SteveMayze/atmega1608_dev/kicad/ATMega1608_Dev/fritzing-part/kicad_svg_plots/board_render.png

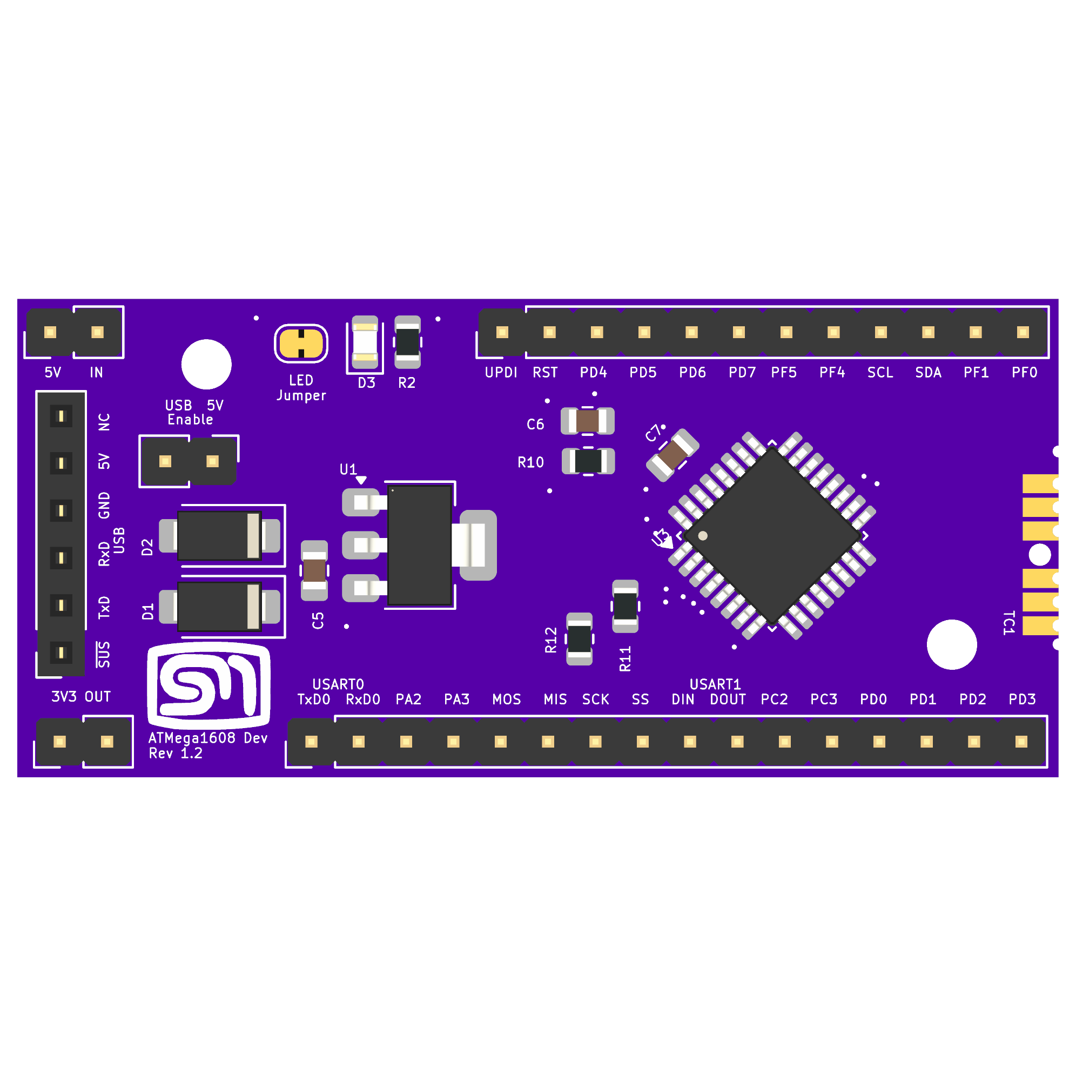
kicad/ATMega1608_Dev/fritzing-part/kicad_svg_plots/board_render.png
