SteveMayze/atmega1608_dev/kicad/doc/PinAllocation.png

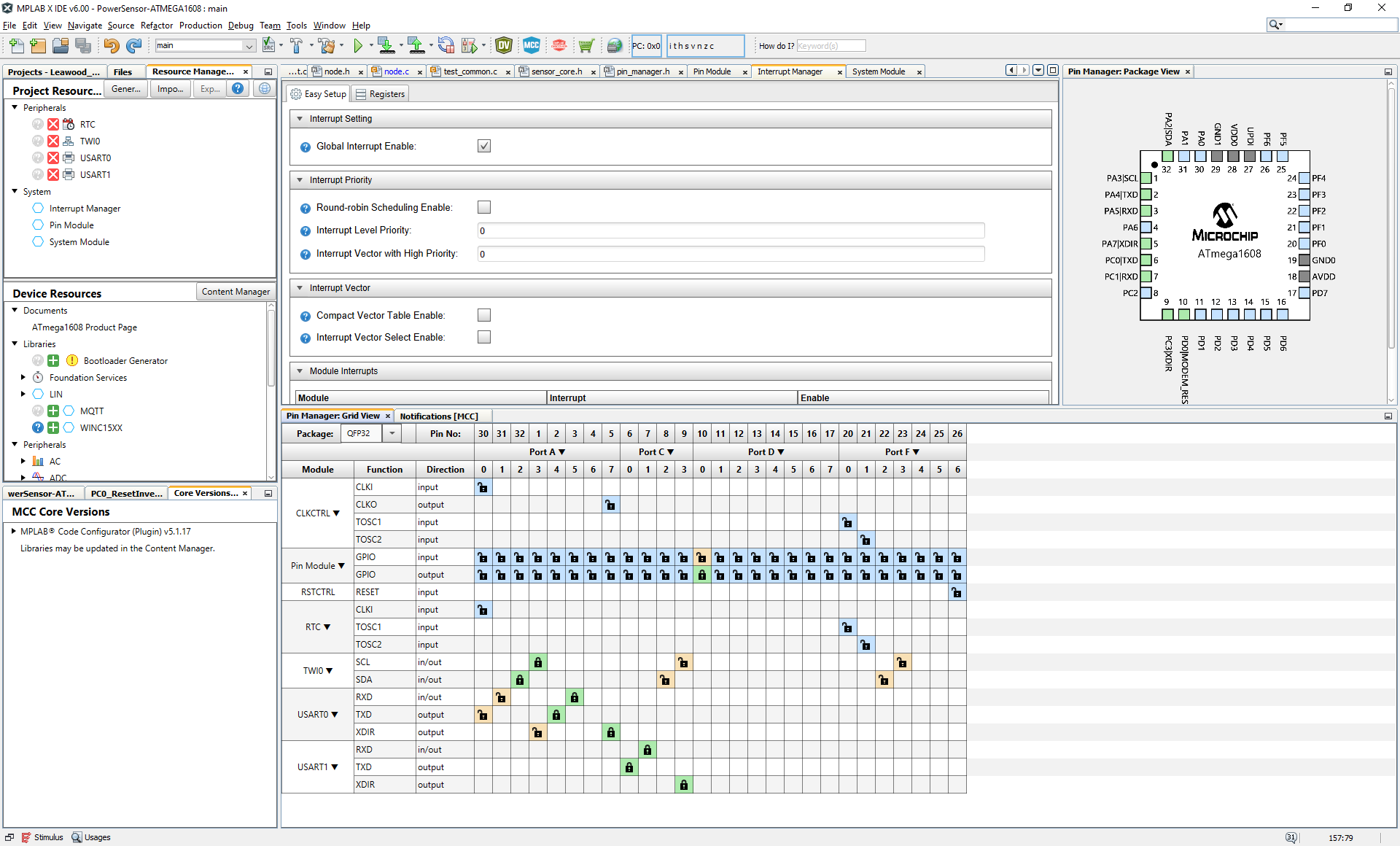
kicad/doc/PinAllocation.png
