SteveMayze/atmega1608_dev/kicad/doc/PinManagerTable.png

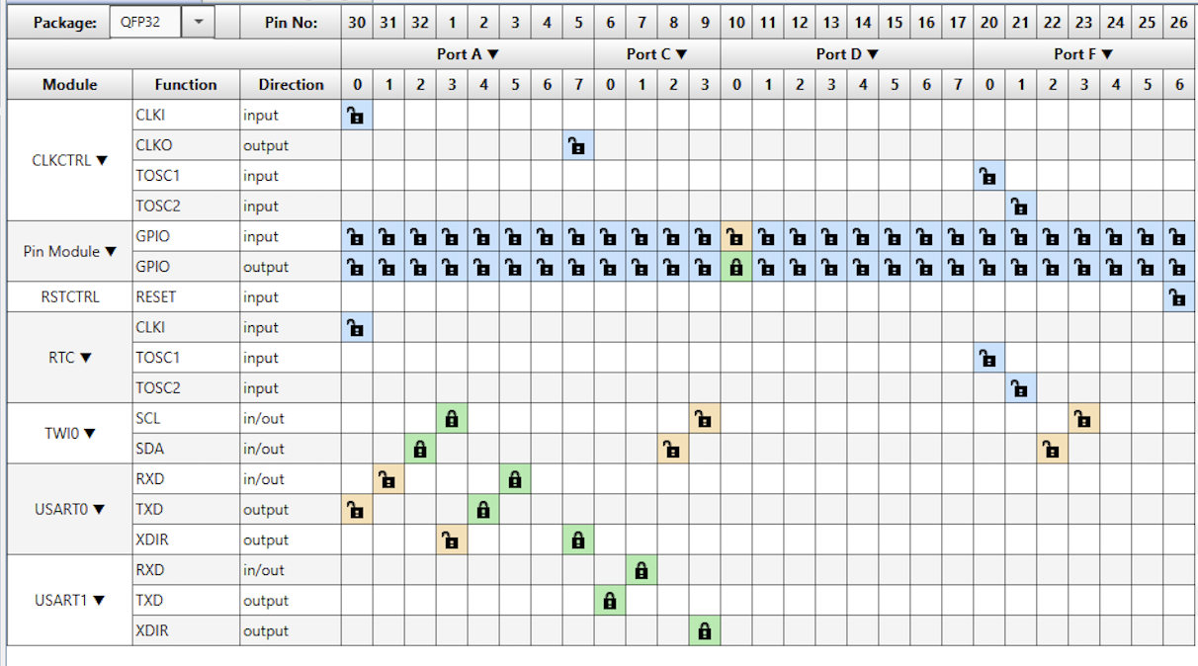
kicad/doc/PinManagerTable.png
