SteveMayze/atmega1608_dev/kicad/doc/USART-Troubleshooting/DeviceManager.png

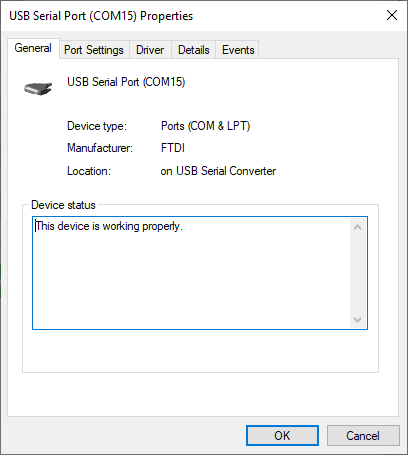
kicad/doc/USART-Troubleshooting/DeviceManager.png
