SteveMayze/atmega1608_dev/kicad/doc/USART-Troubleshooting/DeviceManager_02.png

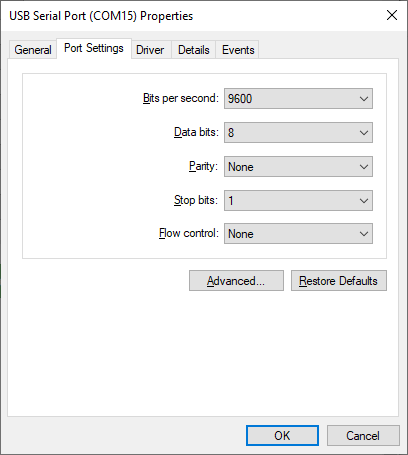
kicad/doc/USART-Troubleshooting/DeviceManager_02.png
