SteveMayze/atmega1608_dev/kicad/doc/USART-Troubleshooting/DeviceManager_03.png

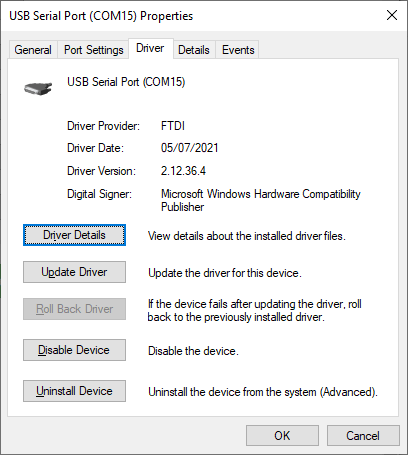
kicad/doc/USART-Troubleshooting/DeviceManager_03.png
