SteveMayze/atmega1608_dev/kicad/doc/CentralCommand-Layout.pdf

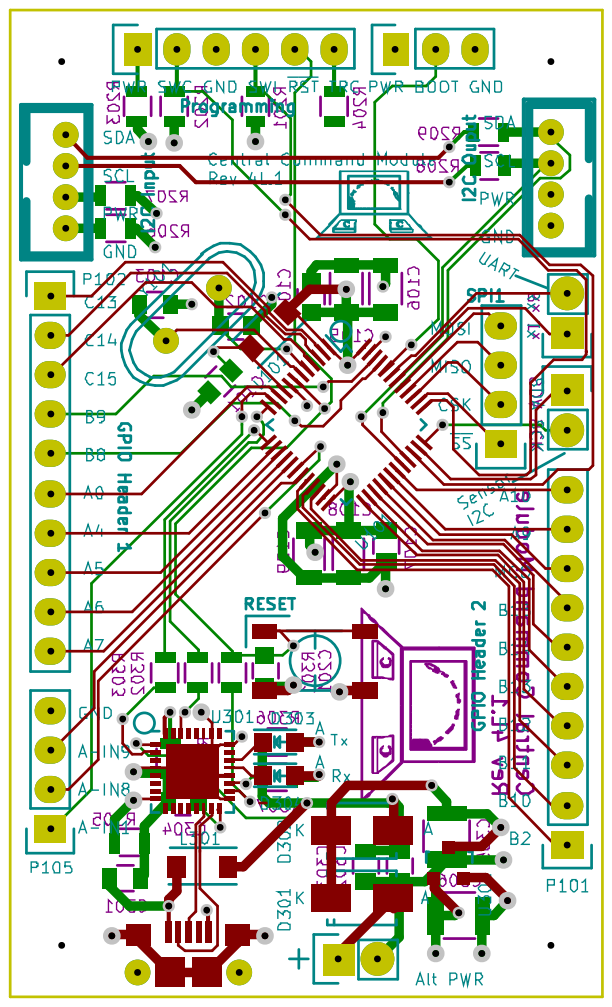
[picture p16: page 1]
