SteveMayze/atmega1608_dev/kicad/doc/SML-LX15IGC-RP-TR.pdf

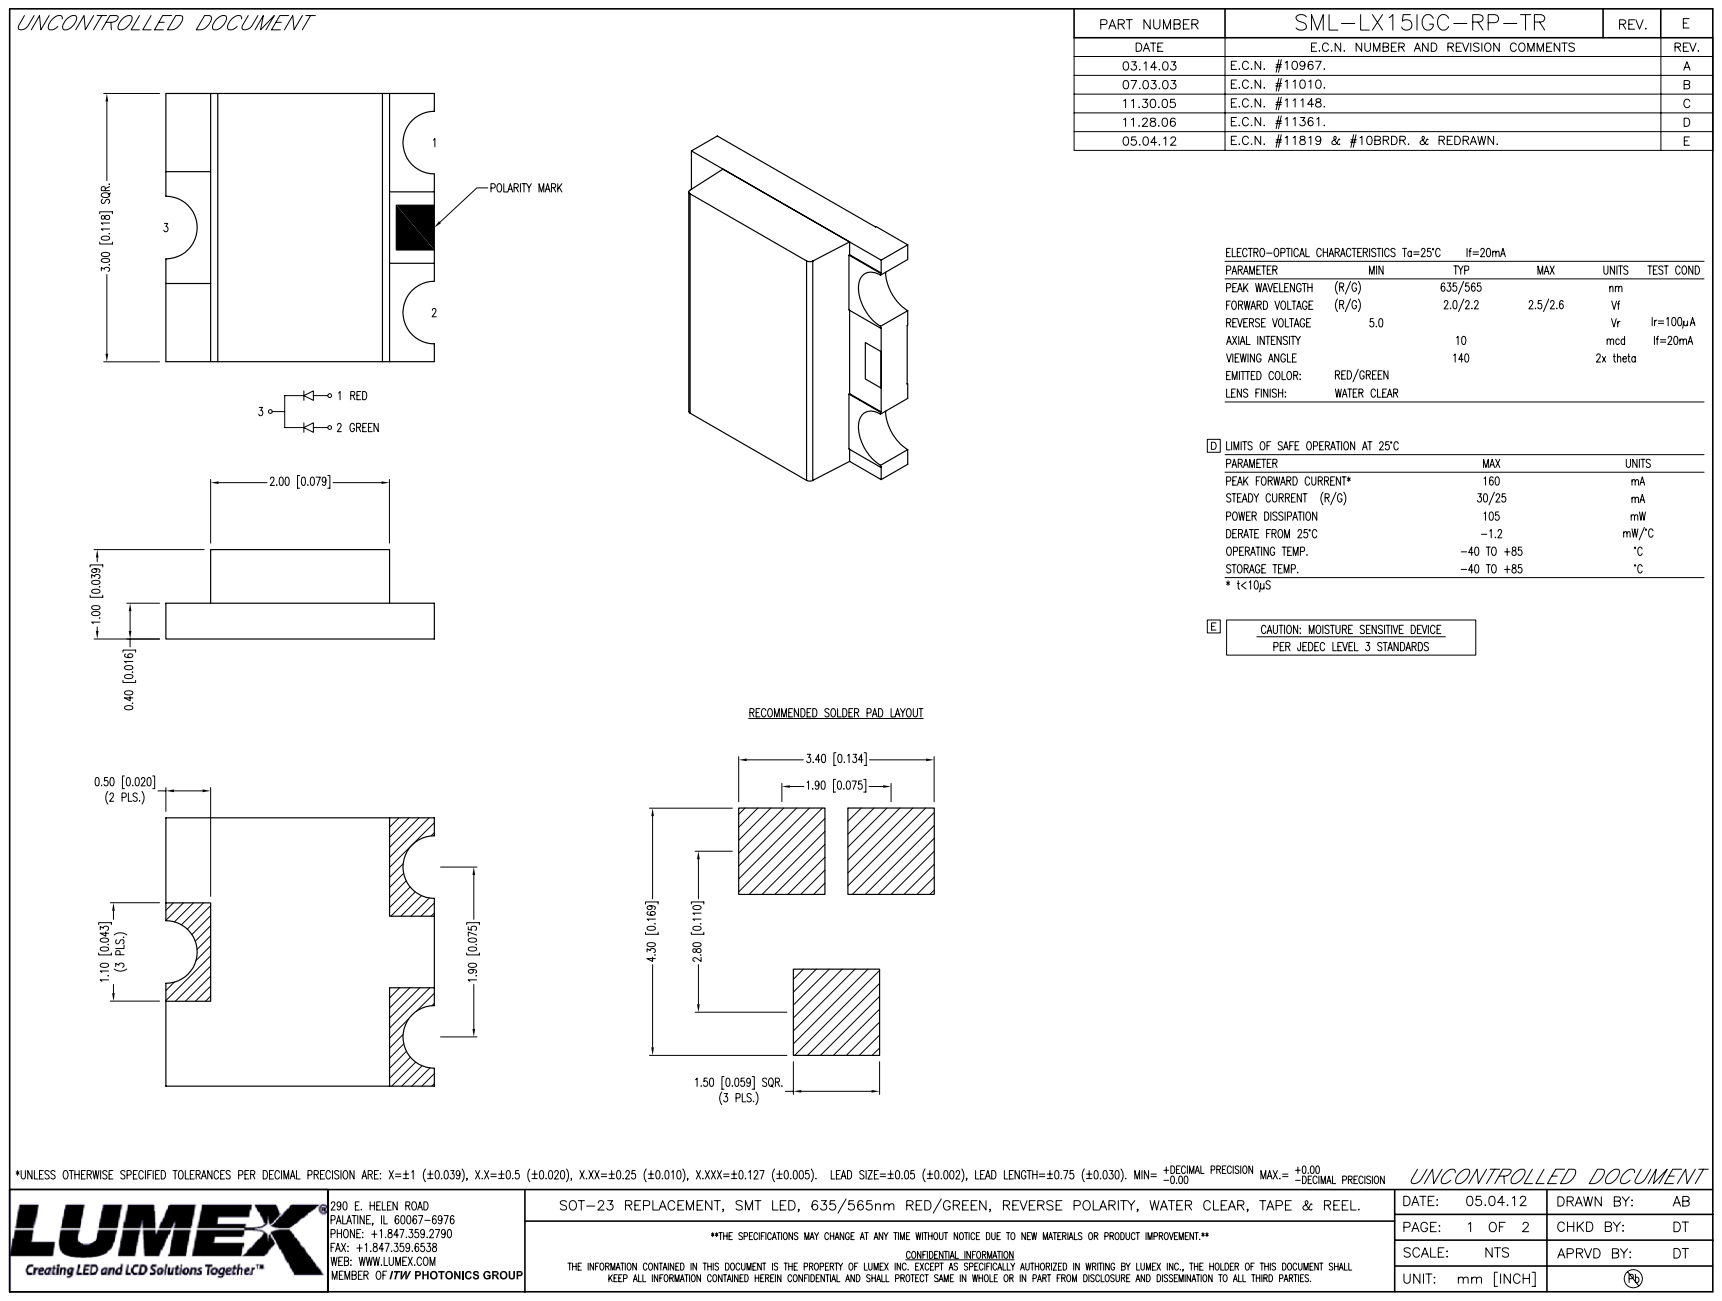
[picture p17: page 1]

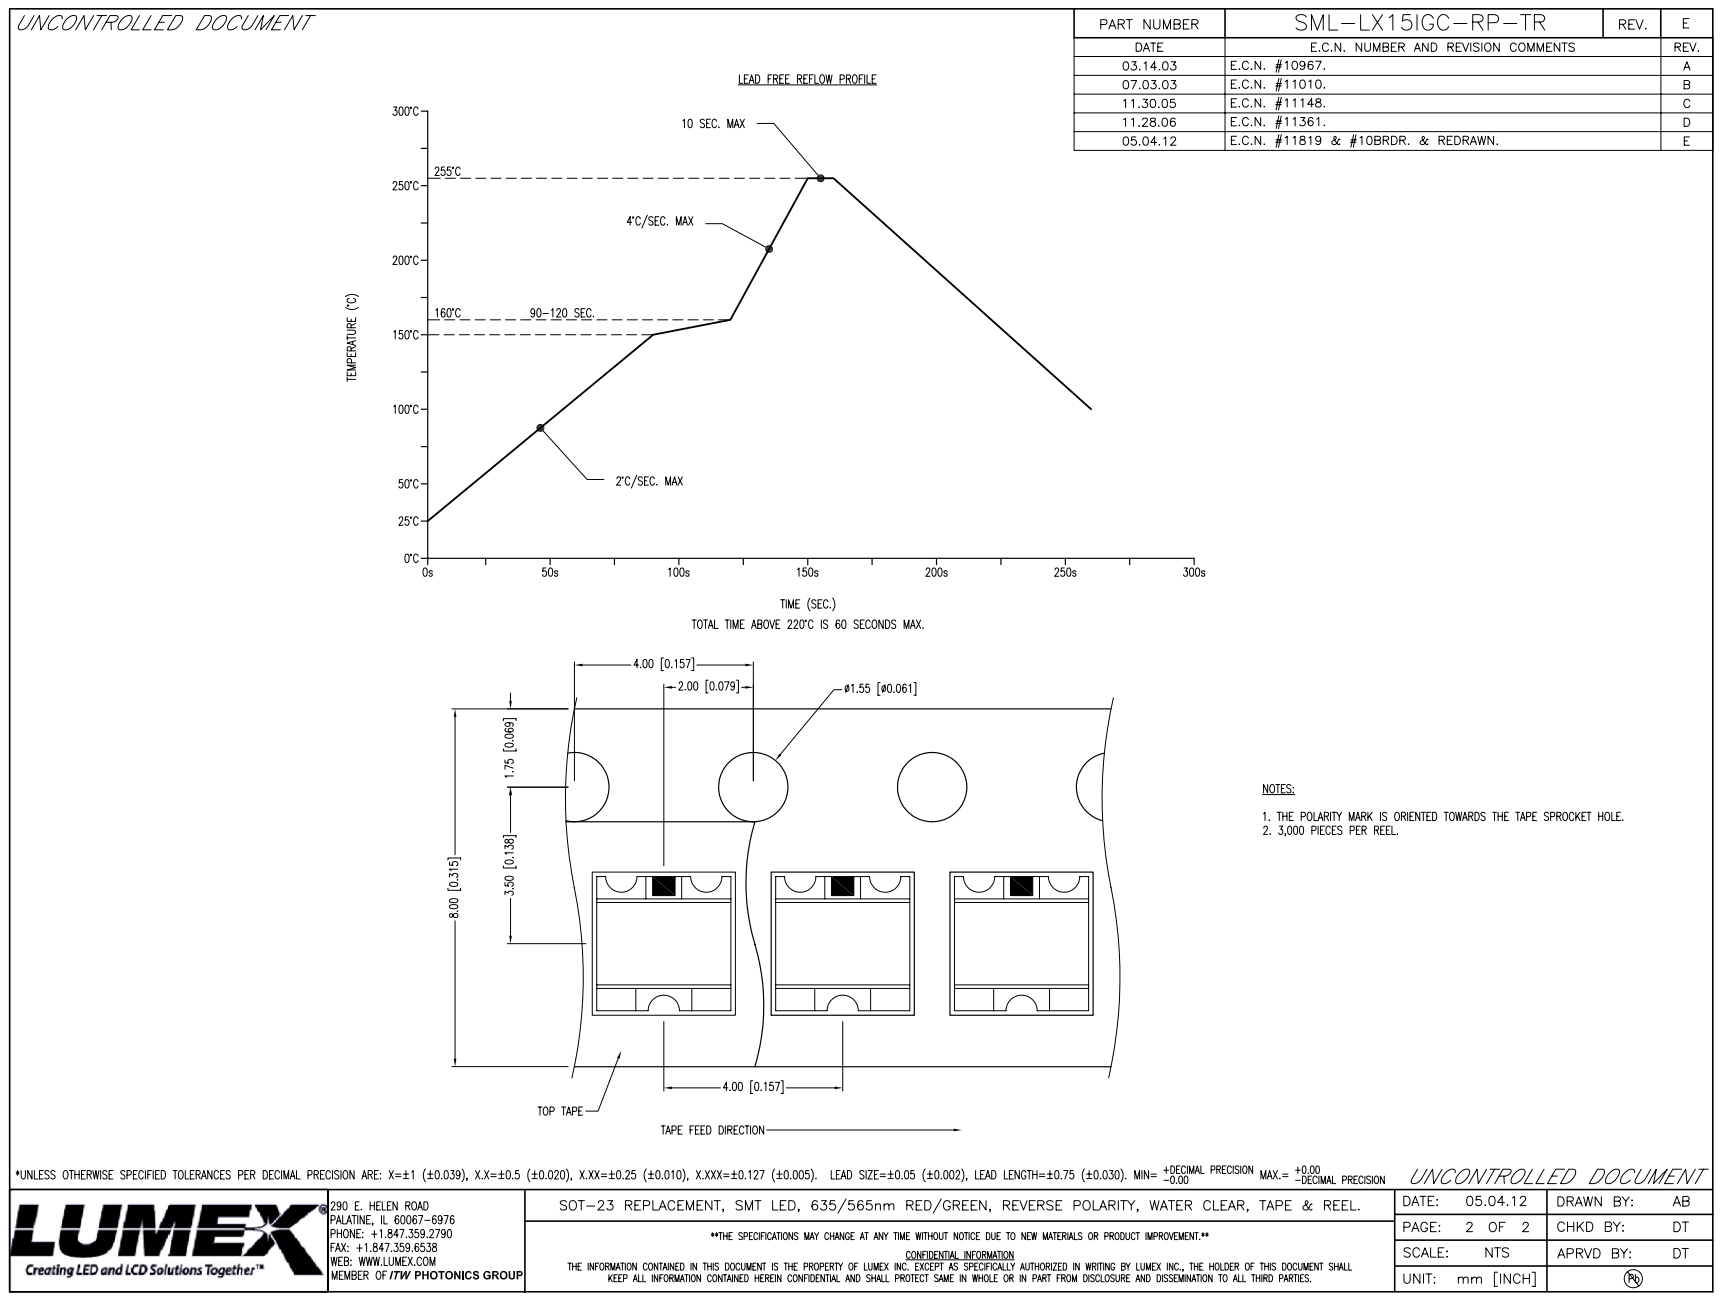
[picture p18: page 2]
